norbert-walter/Windsensor_Yachta/project/cad/Gerber/Bottom_3D_Yachta.png

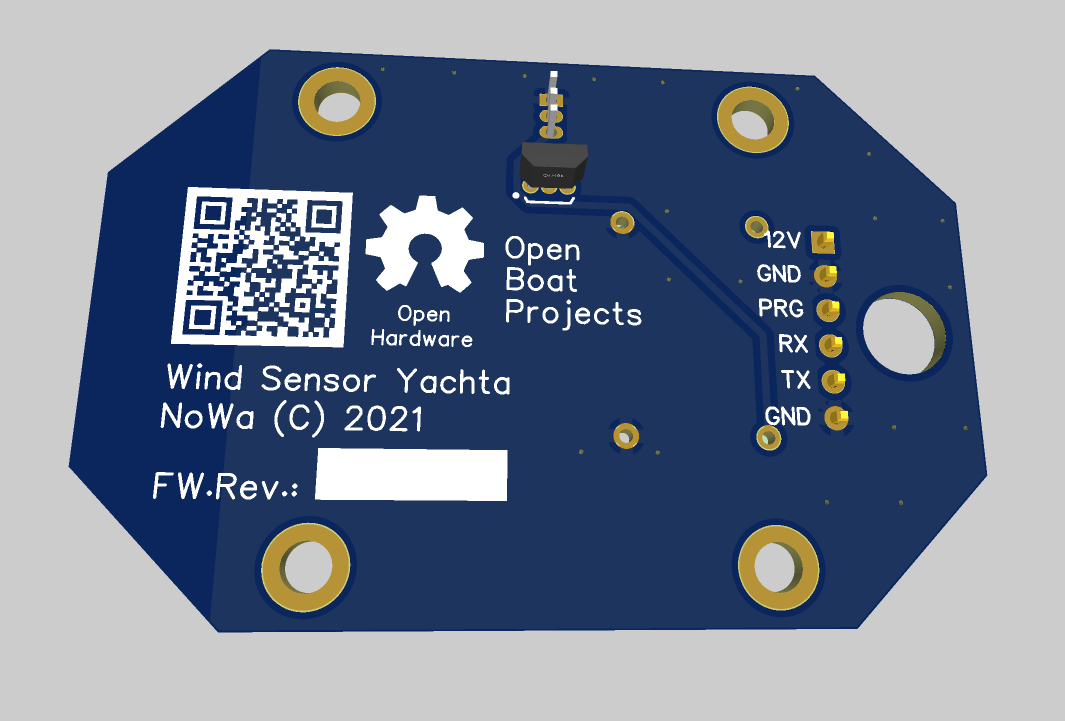
project/cad/Gerber/Bottom_3D_Yachta.png
