norbert-walter/Windsensor_Yachta/project/cad/Gerber/Top_Yachta.png

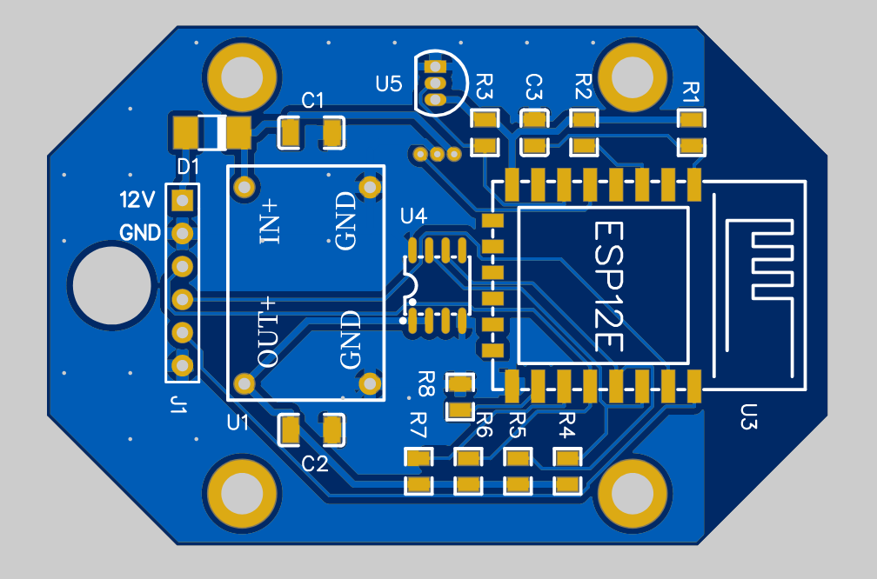
project/cad/Gerber/Top_Yachta.png
