norbert-walter/Windsensor_Yachta/project/pictures/Yachta_Thingiverse/Yachta1.png

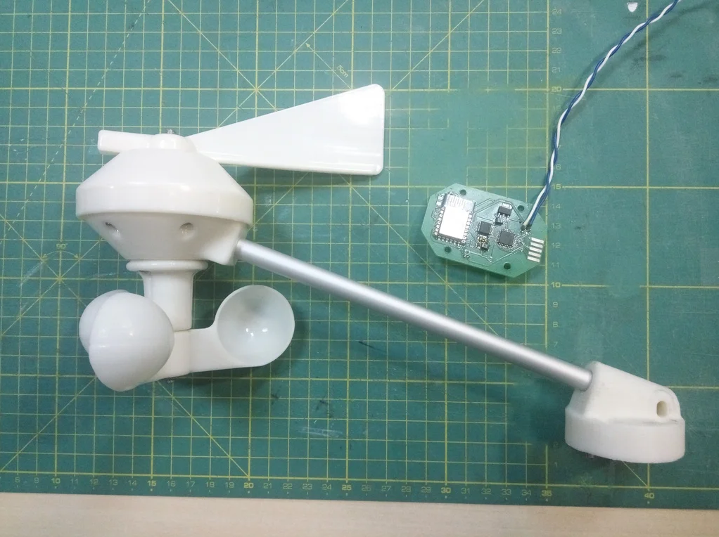
project/pictures/Yachta_Thingiverse/Yachta1.png
