norbert-walter/Windsensor_Yachta/project/pictures/Yachta_Thingiverse/Yachta2.png

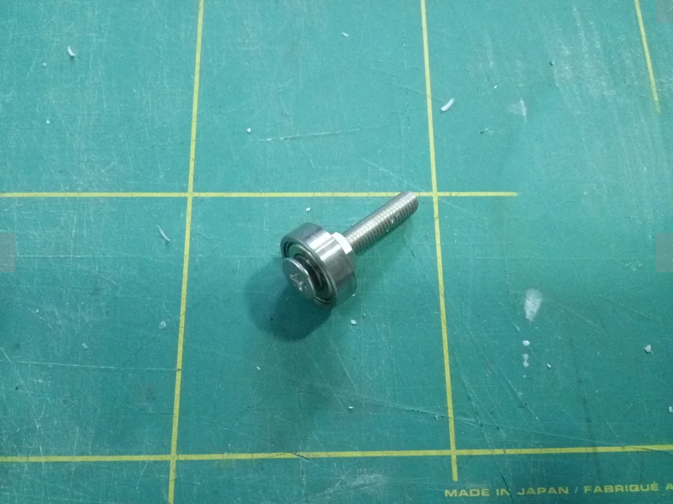
project/pictures/Yachta_Thingiverse/Yachta2.png
