norbert-walter/Windsensor_Yachta/project/pictures/Yachta_Thingiverse/Yachta3.png

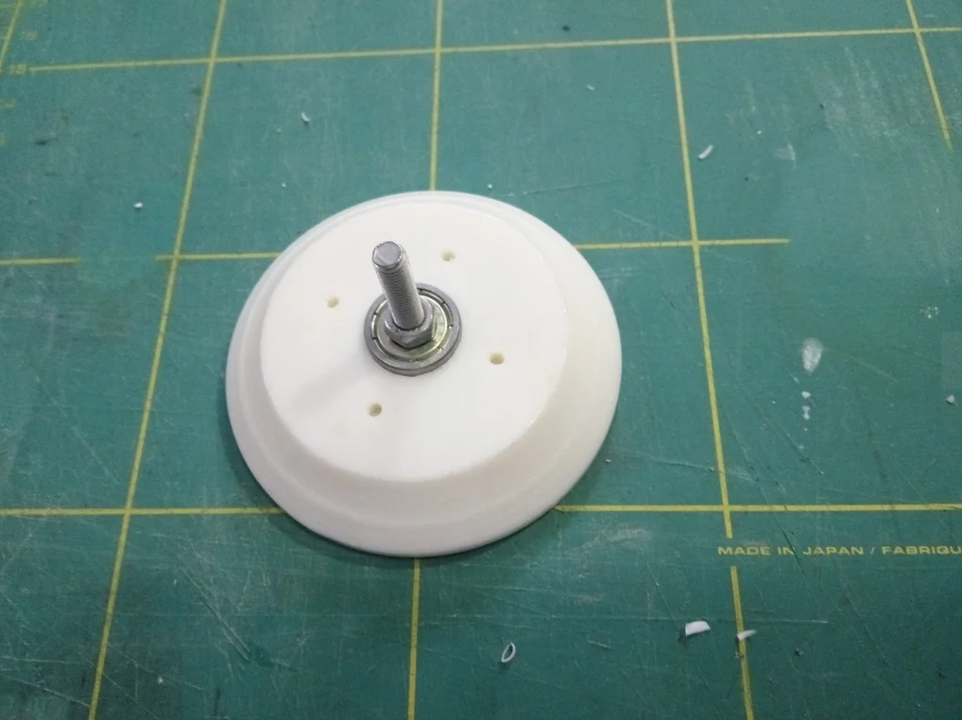
project/pictures/Yachta_Thingiverse/Yachta3.png
