norbert-walter/Windsensor_Yachta/project/pictures/Yachta_Thingiverse/Yachta5.png

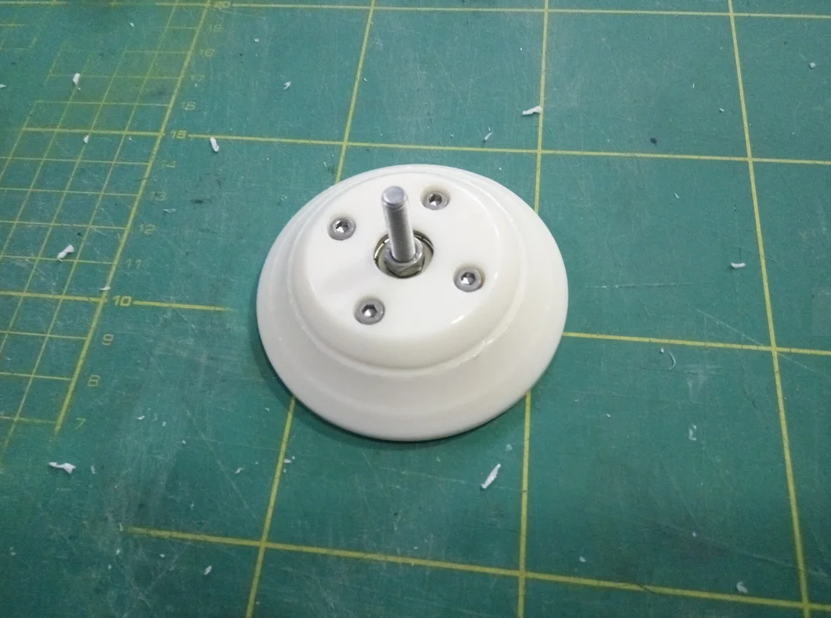
project/pictures/Yachta_Thingiverse/Yachta5.png
