norbert-walter/Windsensor_Yachta/project/pictures/Yachta_Thingiverse/Yachta7.png

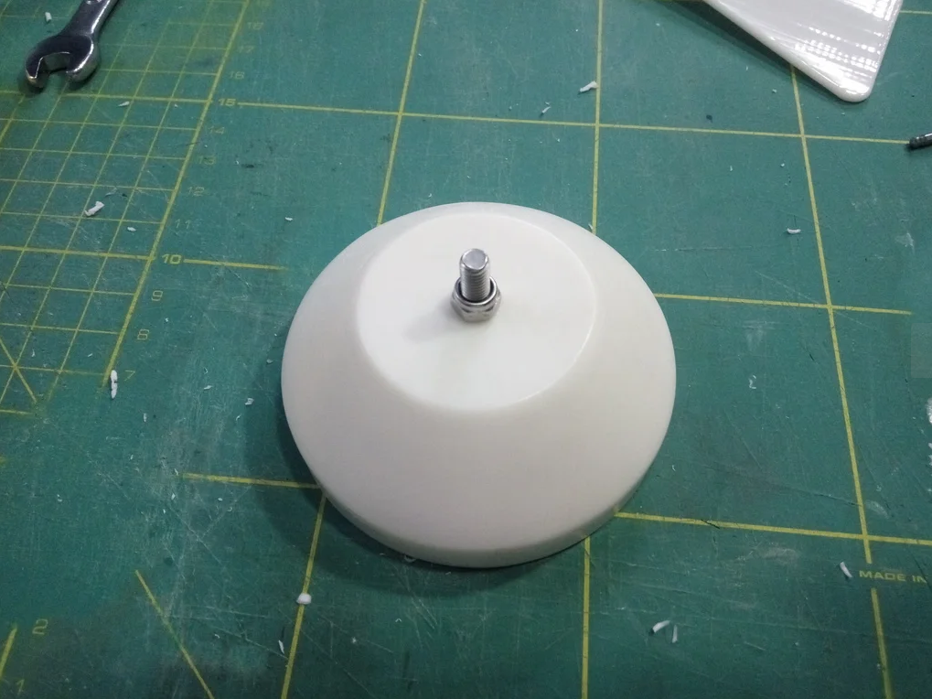
project/pictures/Yachta_Thingiverse/Yachta7.png
