norbert-walter/Windsensor_Yachta/project/pictures/Yachta_Thingiverse/Yachta8.png

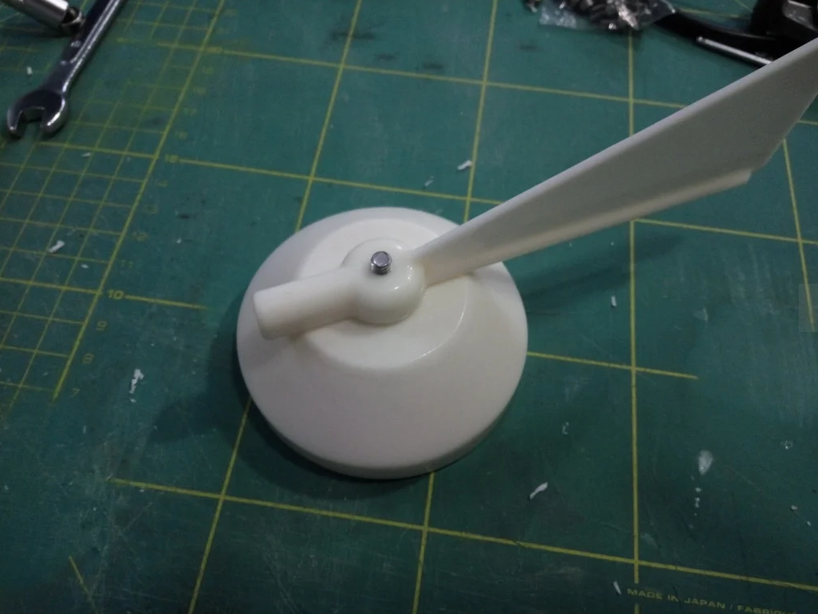
project/pictures/Yachta_Thingiverse/Yachta8.png
