norbert-walter/Windsensor_Yachta/project/pictures/Yachta_Thingiverse/Yachta10.png

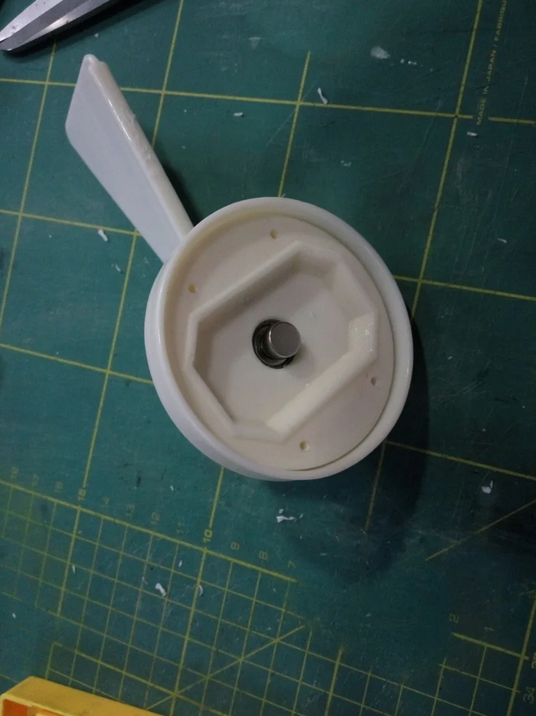
project/pictures/Yachta_Thingiverse/Yachta10.png
