norbert-walter/Windsensor_Yachta/project/pictures/Yachta_Thingiverse/Yachta11.png

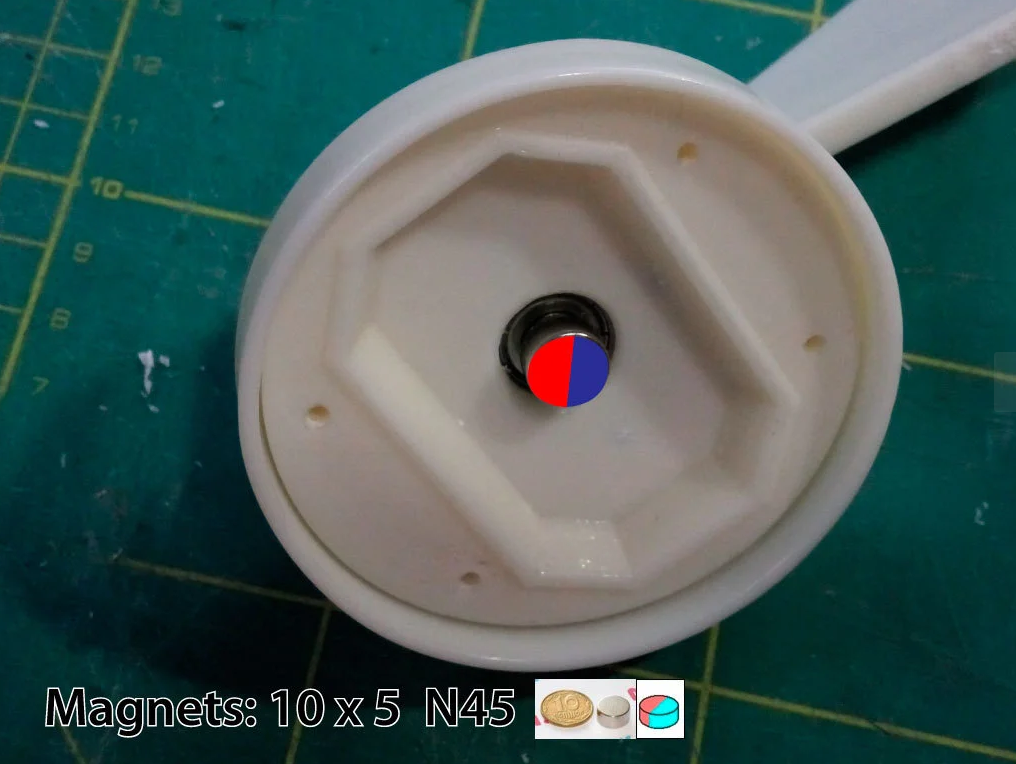
project/pictures/Yachta_Thingiverse/Yachta11.png
