norbert-walter/Windsensor_Yachta/project/pictures/Yachta_Thingiverse/Yachta13.png

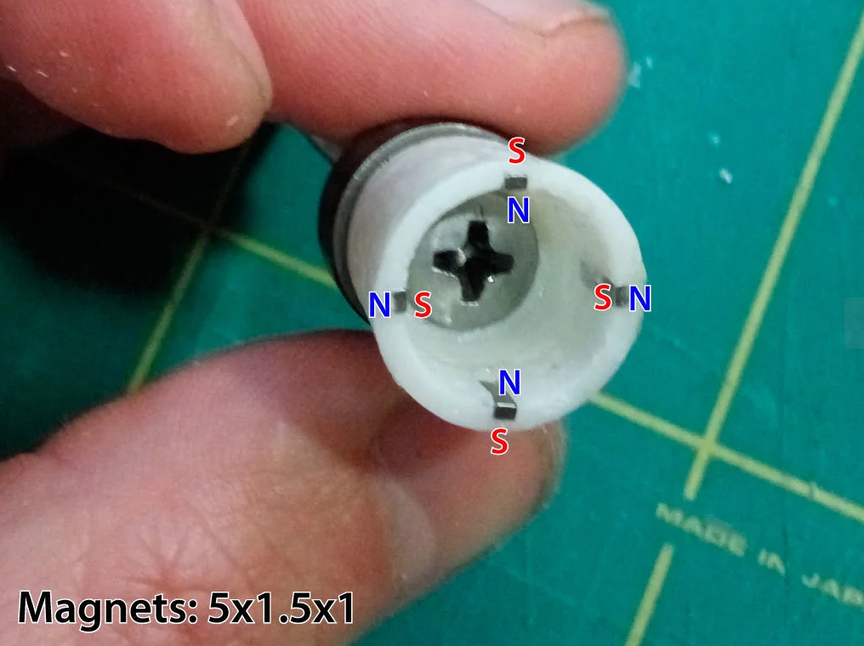
project/pictures/Yachta_Thingiverse/Yachta13.png
