norbert-walter/Windsensor_Yachta/project/pictures/Yachta_Thingiverse/Yachta14.png

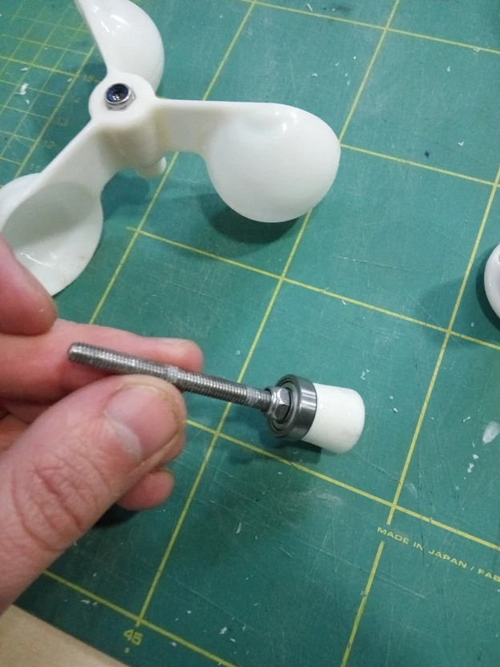
project/pictures/Yachta_Thingiverse/Yachta14.png
