norbert-walter/Windsensor_Yachta/project/pictures/Yachta_Thingiverse/Yachta15.png

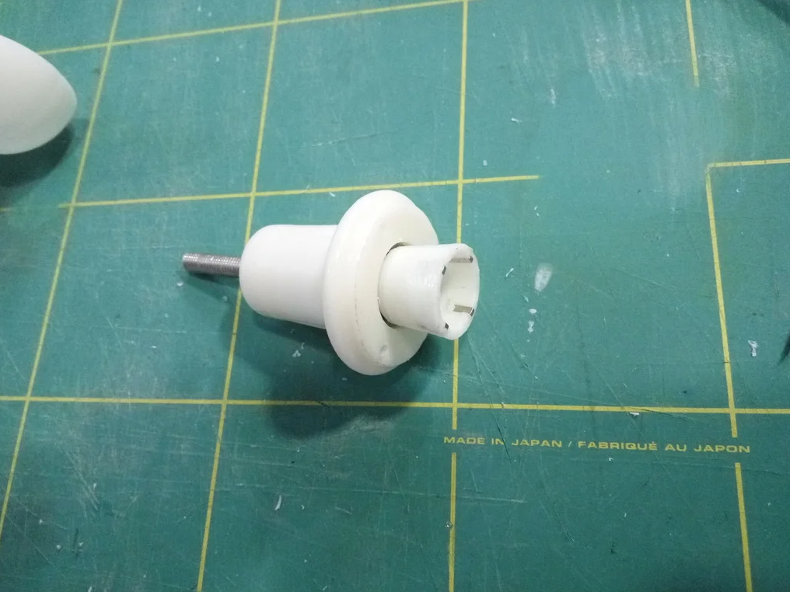
project/pictures/Yachta_Thingiverse/Yachta15.png
