norbert-walter/Windsensor_Yachta/project/pictures/Yachta_Thingiverse/Yachta16.png

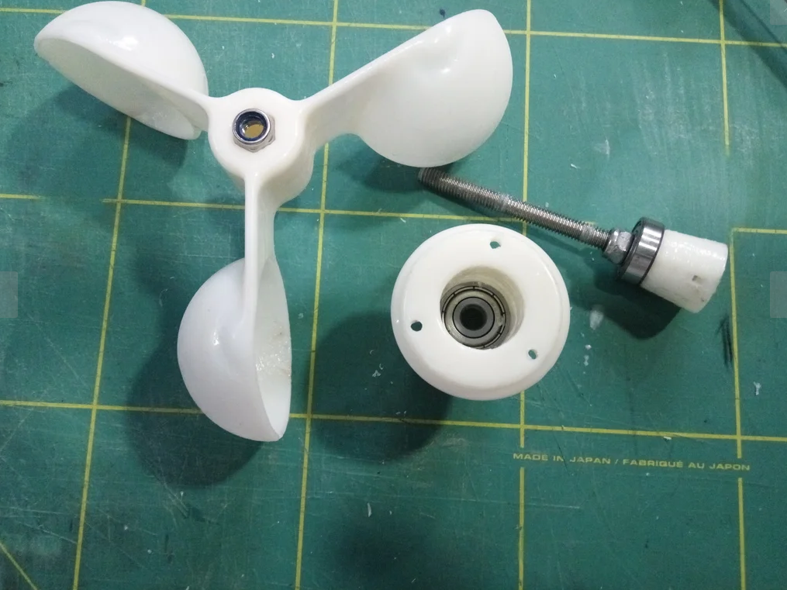
project/pictures/Yachta_Thingiverse/Yachta16.png
