norbert-walter/Windsensor_Yachta/project/pictures/Yachta_Thingiverse/Yachta17.png

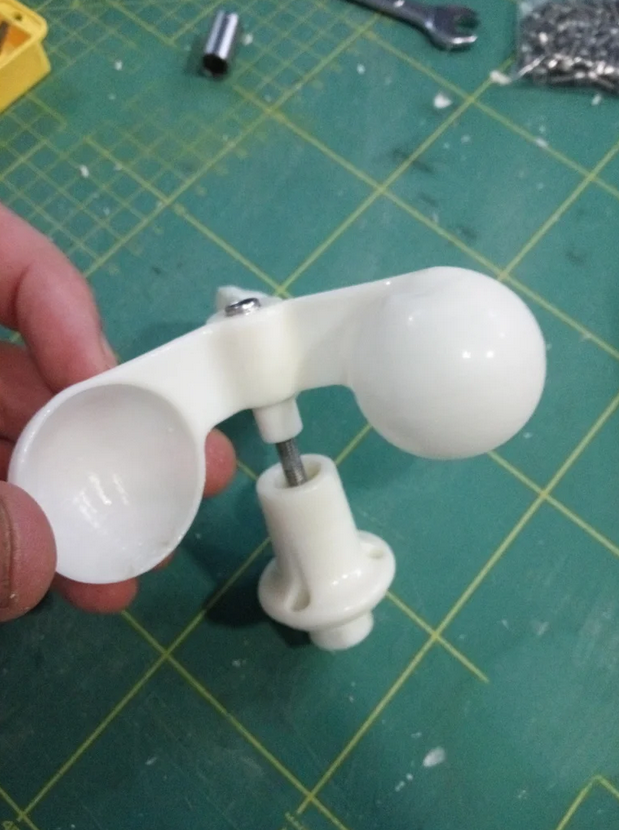
project/pictures/Yachta_Thingiverse/Yachta17.png
