norbert-walter/Windsensor_Yachta/project/pictures/Yachta_Thingiverse/Yachta18.png

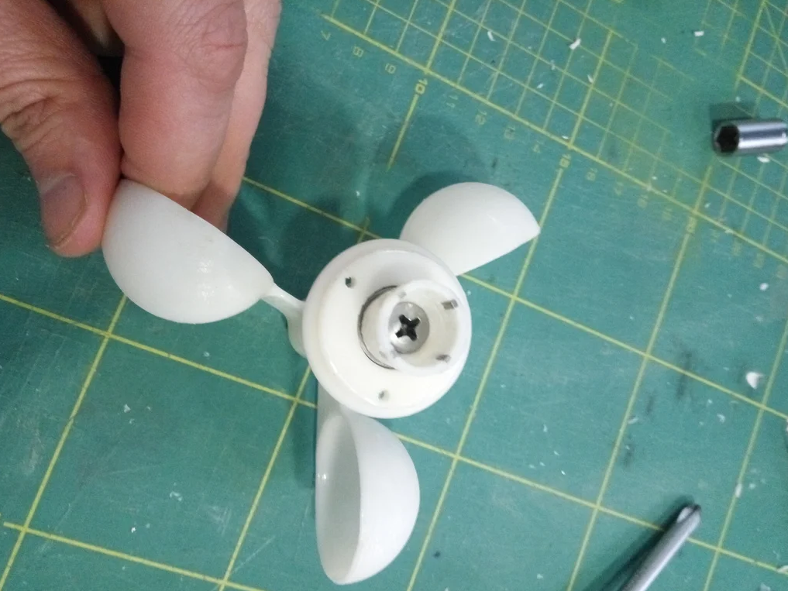
project/pictures/Yachta_Thingiverse/Yachta18.png
