norbert-walter/Windsensor_Yachta/project/pictures/Yachta_Thingiverse/Yachta19.png

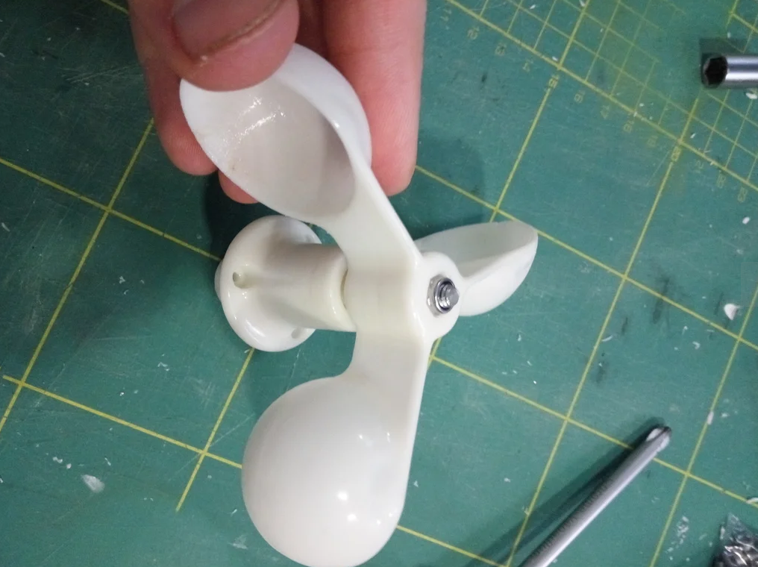
project/pictures/Yachta_Thingiverse/Yachta19.png
