norbert-walter/Windsensor_Yachta/project/pictures/Yachta_Thingiverse/Yachta20.png

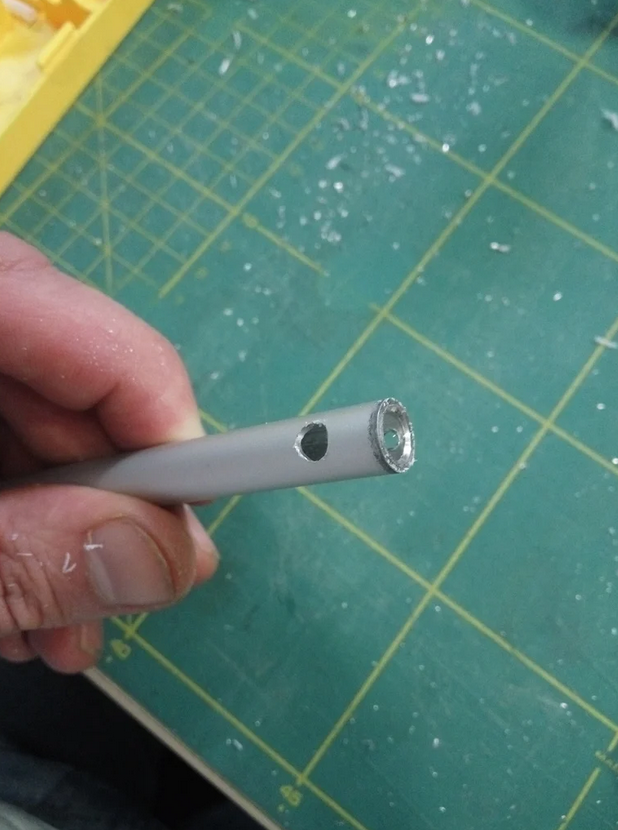
project/pictures/Yachta_Thingiverse/Yachta20.png
