norbert-walter/Windsensor_Yachta/project/pictures/Yachta_Thingiverse/Yachta21.png

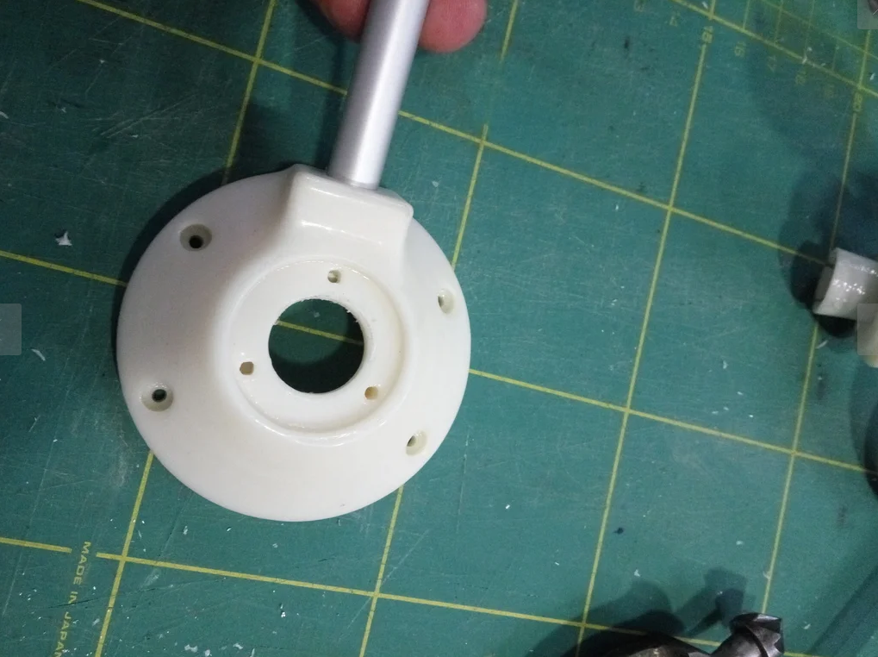
project/pictures/Yachta_Thingiverse/Yachta21.png
