norbert-walter/Windsensor_Yachta/project/pictures/Yachta_Thingiverse/Yachta22.png

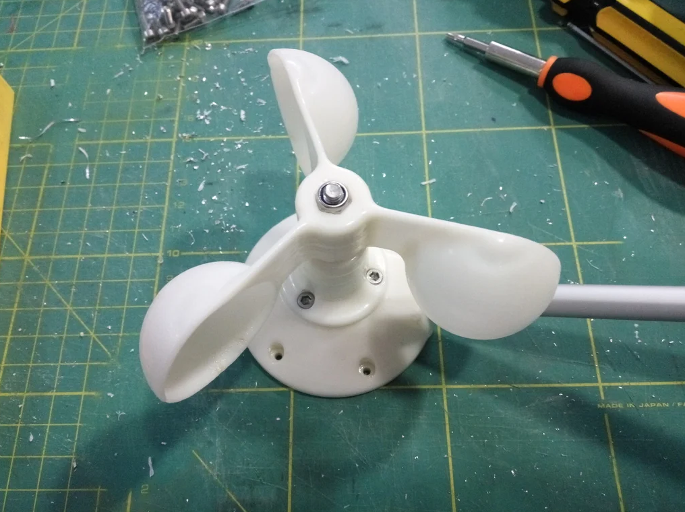
project/pictures/Yachta_Thingiverse/Yachta22.png
