norbert-walter/Windsensor_Yachta/project/pictures/Yachta_Thingiverse/Yachta23.png

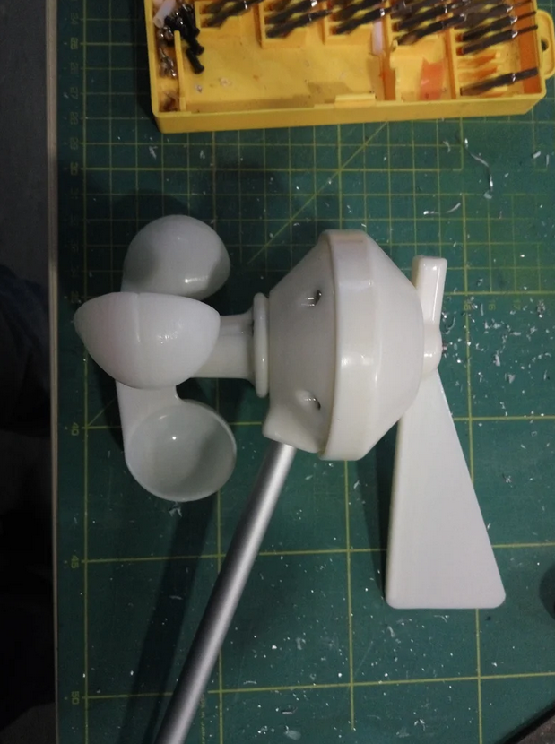
project/pictures/Yachta_Thingiverse/Yachta23.png
