norbert-walter/Windsensor_Yachta/project/cad/3D-Parts/base_power.stl

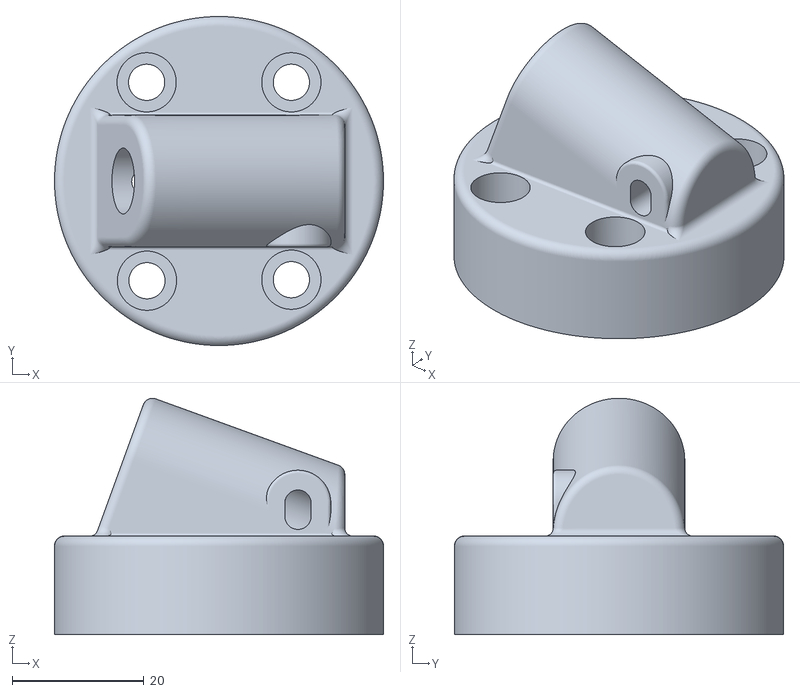
[picture p48: CAD file, 2023-07-21]
project/cad/3D-Parts/base_power.stl
50.0 x 50.0 x 35.9
