norbert-walter/Windsensor_Yachta/project/cad/Mechanics/IGES/Loeffel_spitz v1.iges

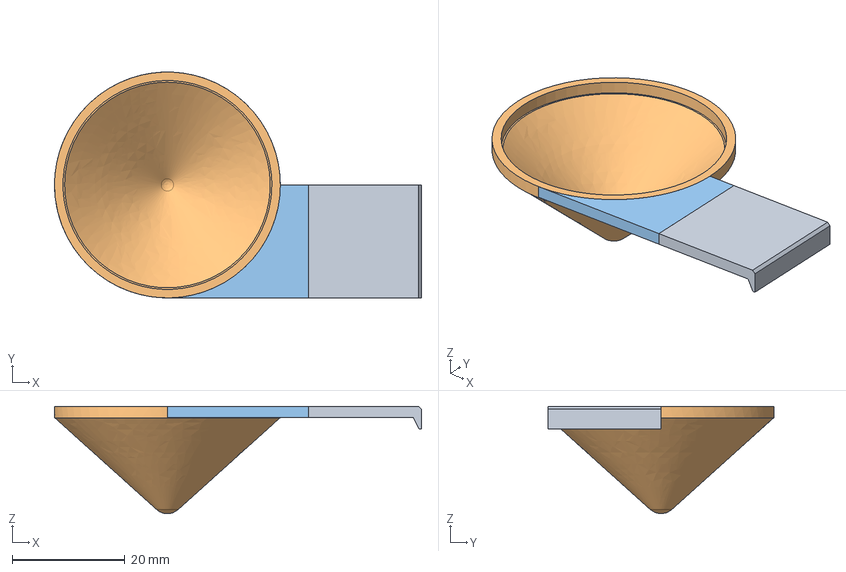
[picture p49: CAD file, 2023-07-21]
project/cad/Mechanics/IGES/Loeffel_spitz v1.iges
65.0 x 40.0 x 19.0 mm
