norbert-walter/Windsensor_Yachta/project/cad/Mechanics/IGES/Magnethalter.iges

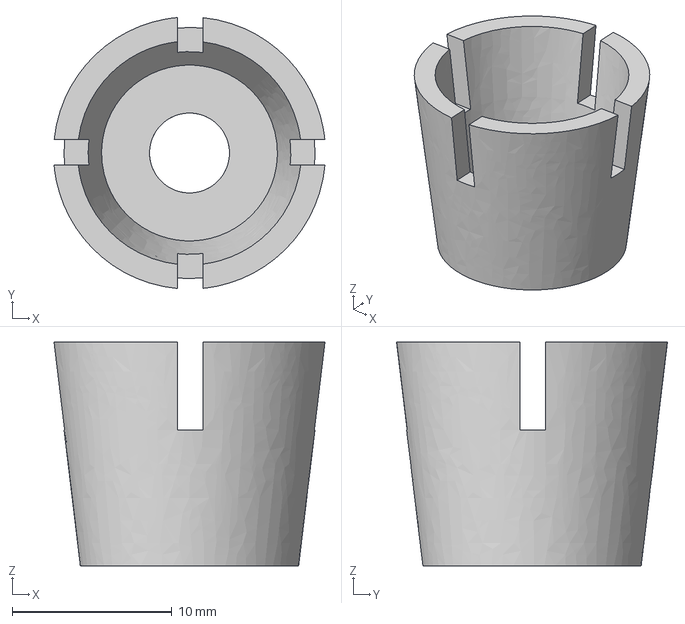
[picture p50: CAD file, 2023-07-21]
project/cad/Mechanics/IGES/Magnethalter.iges
17.0 x 17.0 x 14.0 mm
