norbert-walter/Windsensor_Yachta/project/cad/3D-Parts/top_1.stl

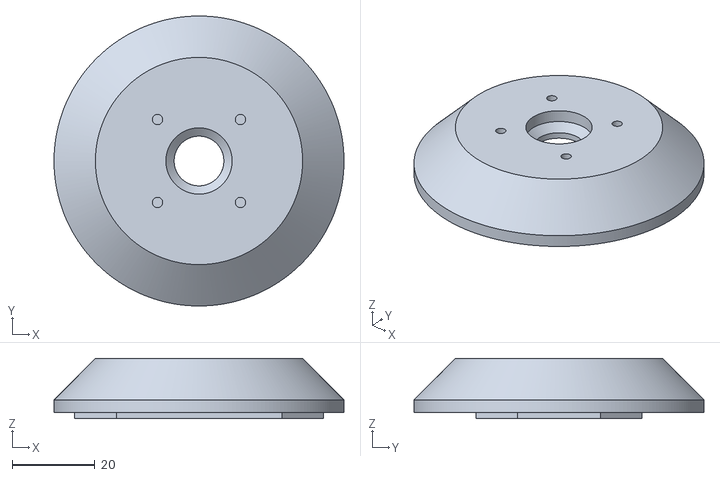
[picture p51: CAD file, 2023-07-21]
project/cad/3D-Parts/top_1.stl
70.0 x 70.0 x 14.5
