norbert-walter/Windsensor_Yachta/project/cad/3D-Parts/top_2.stl

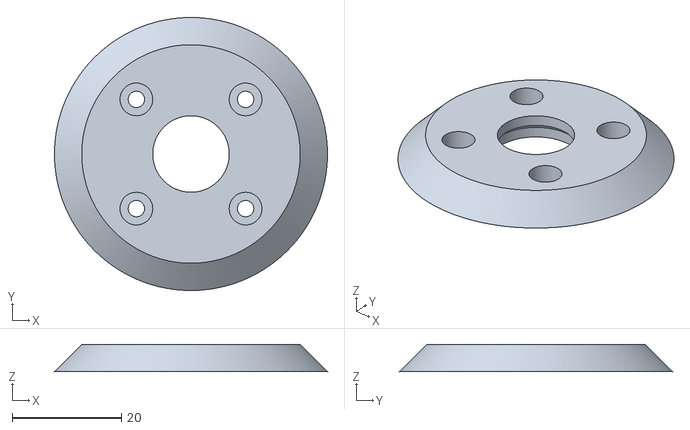
[picture p52: CAD file, 2023-07-21]
project/cad/3D-Parts/top_2.stl
50.0 x 50.0 x 5.00
