norbert-walter/Windsensor_Yachta/project/cad/3D-Parts/Print_Position.jpg

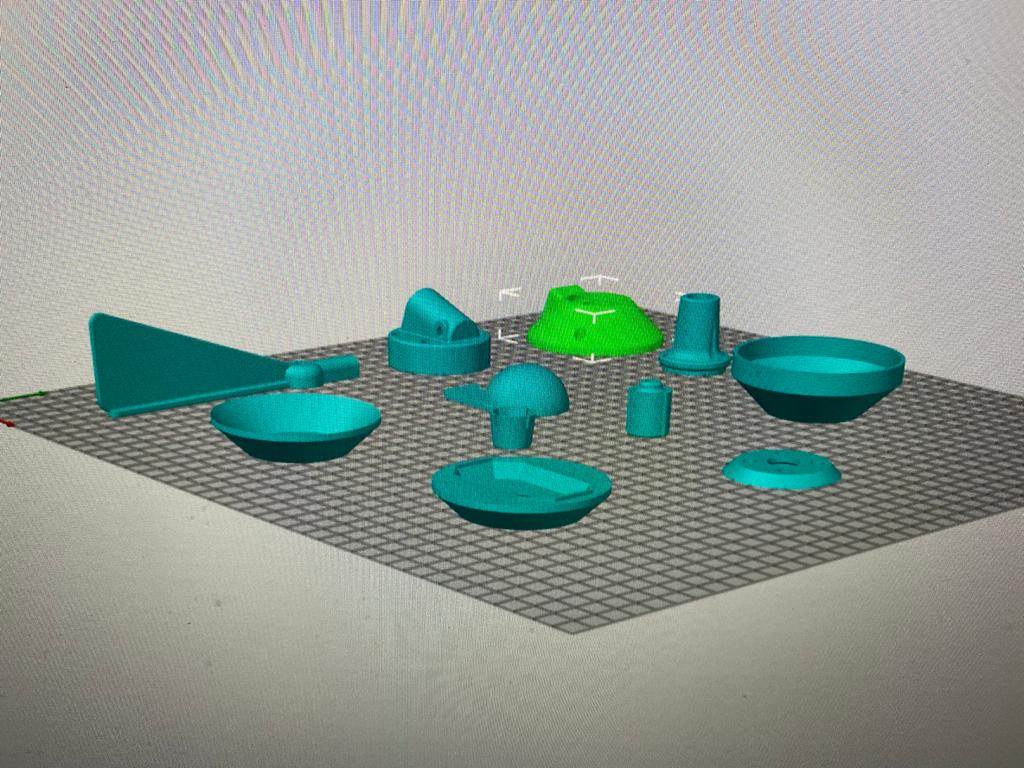
project/cad/3D-Parts/Print_Position.jpg
