norbert-walter/Windsensor_Yachta/project/pictures/Yachta_Thingiverse/Assembly2.png

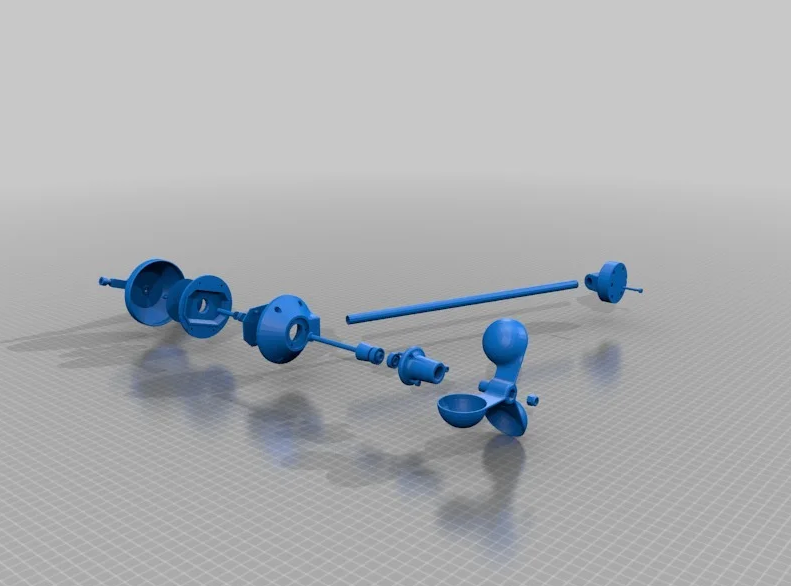
project/pictures/Yachta_Thingiverse/Assembly2.png
