norbert-walter/Windsensor_Yachta/project/pictures/Yachta_Thingiverse/Assembly.png

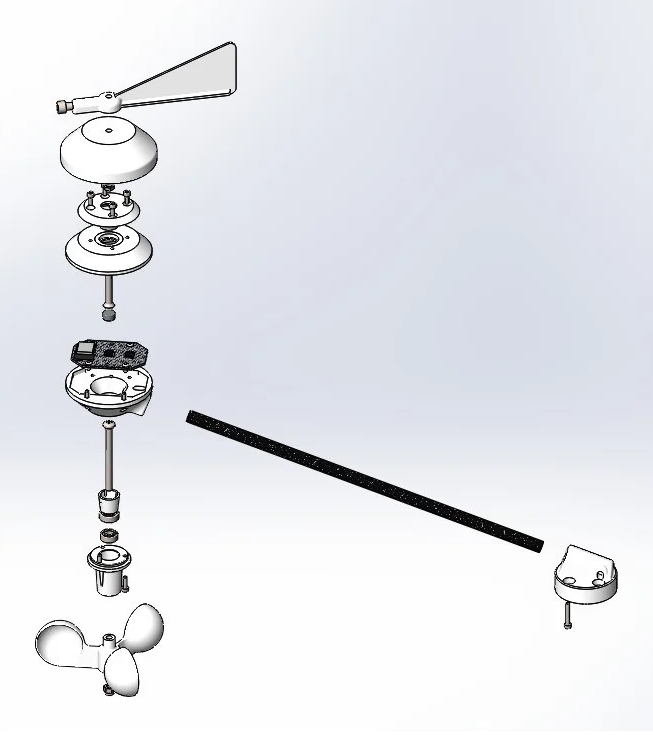
project/pictures/Yachta_Thingiverse/Assembly.png
