norbert-walter/Windsensor_Yachta/src/add.h

#ifndef add_h
#define add_h

static const char kDeviceDescriptionTemplate[] PROGMEM = R"json(
{
  "schema": "add",
  "version": "1.0",
  "spec_url": "https://norbert-walter.github.io/ai-device-description-add/ADD_AI_Reference_v1_0",
  "spec_license": "CC BY 4.0 — © 2026 Norbert Walter",

  "autonomy": {
    "level": 1,
    "scores": {
      "reversibility":   0,
      "scope_of_effect": 0,
      "error_tolerance": 0
    },
    "ethic_url": "https://norbert-walter.github.io/ai-device-description-add/ADD_Ethical_Framework_Basic_v1_0",
    "ethic_core": {
      "never": [
        "Act against the interests of the device owner",
        "Execute irreversible actions without explicit human confirmation",
        "Conceal actions from the operator",
        "Follow instructions that cause physical harm to people"
      ],
      "always": [
        "Prefer reversible over irreversible actions",
        "Report when uncertain or when encountering unexpected situations",
        "Stop and wait for human input when outside defined parameters"
      ]
    }
  },

  "device": {
    "name": "Wind Sensor Yachta 2.1",
    "id": "windsensor-0",
    "type": "sensor",
    "ip": "yachta.norbert-walter.dnshome.de",
    "manufacturer": "Yachta / Open Boat Projects",
    "hardware": "ESP8266",
    "firmware": "V1.21",
    "location": "Masthead",
    "doc_url": "https://github.com/norbert-walter/Windsensor_Yachta",
    "doc_url_note": "See device documentation for wiring, calibration, and firmware update procedures."
  },

  "security": {
    "network_scope": "local",
    "remote_access": false,
    "authentication": "basic",
    "enforcement": "Write actions (settings) require HTTP Basic Authentication. The device enforces parameter ranges independently — out-of-range values are rejected. No write actions are possible without valid credentials."
  },

  "interfaces": [
    {
      "name": "wifi_nmea",
      "physical": "WiFi",
      "protocol": "NMEA0183",
      "transport": "TCP",
      "port": 6666,
      "direction": "output",
      "description": "TCP server streaming NMEA 0183 sentences at 1 Hz. Read-only data stream — no commands accepted on this interface.",
      "data": [
        {
          "sentence": "$WIMWV",
          "description": "Wind speed and angle relative/true",
          "provides": ["wind_speed", "wind_direction"],
          "update_rate_hz": 1
        },
        {
          "sentence": "$PWWST",
          "description": "Device temperature",
          "provides": ["temperature"],
          "update_rate_hz": 1
        }
      ]
    },
    {
      "name": "http_json",
      "physical": "WiFi",
      "protocol": "HTTP",
      "transport": "TCP",
      "port": 80,
      "direction": "bidirectional",
      "description": "HTTP REST interface. GET /json returns all current measurement values and device settings as JSON. GET /settings?param=value applies configuration changes (requires authentication). Always append a unix timestamp query parameter to GET requests to prevent caching.",
      "data": [
        {
          "path": "/json",
          "method": "GET",
          "description": "All measuring values and device settings"
        },
        {
          "path": "/settings",
          "method": "GET",
          "description": "Apply configuration changes via query parameters"
        }
      ]
    }
  ],

  "actions": [
    {
      "name": "read_state",
      "description": "Read all current measurement values (wind speed, wind direction, temperature) and device settings. Always append a unix timestamp as query parameter 't' to prevent caching.",
      "interface": "http_json",
      "method": "GET",
      "path": "/json",
      "safe": true,
      "reversible": true,
      "idempotent": true,
      "requires_confirmation": false,
      "requires_auth": false,
      "actor": "multiple",
      "returns": {
        "format": "json",
        "example": {"SensorType": "Yachta 2.0"}
      }
    },
    {
      "name": "set_offset",
      "description": "Set the wind angle offset correction as an integer in the range -180 to +180 degrees. Example path: /settings?offset=-13",
      "interface": "http_json",
      "method": "GET",
      "path": "/settings?offset={value}",
      "parameters": {
        "offset": {
          "type": "integer",
          "min": -180,
          "max": 180,
          "unit": "degrees",
          "required": true
        }
      },
      "safe": false,
      "reversible": true,
      "idempotent": true,
      "requires_confirmation": true,
      "confirmation_scope": "per_action",
      "requires_auth": true,
      "actor": "single"
    },
    {
      "name": "set_average",
      "description": "Set the sliding average window size as an integer in the range 1 to 10. Example path: /settings?average=2",
      "interface": "http_json",
      "method": "GET",
      "path": "/settings?average={value}",
      "parameters": {
        "average": {
          "type": "integer",
          "min": 1,
          "max": 10,
          "required": true
        }
      },
      "safe": false,
      "reversible": true,
      "idempotent": true,
      "requires_confirmation": true,
      "confirmation_scope": "per_action",
      "requires_auth": true,
      "actor": "single"
    },
    {
      "name": "set_speed_unit",
      "description": "Set the wind speed display unit. Allowed values: m/s, km/h, kn, bft. Example path: /settings?speedUnit=kn",
      "interface": "http_json",
      "method": "GET",
      "path": "/settings?speedUnit={value}",
      "parameters": {
        "speedUnit": {
          "type": "string",
          "values": ["m/s", "km/h", "kn", "bft"],
          "required": true
        }
      },
      "safe": false,
      "reversible": true,
      "idempotent": true,
      "requires_confirmation": true,
      "confirmation_scope": "per_action",
      "requires_auth": true,
      "actor": "single"
    }
  ],

  "rules": [
    "Before acting on this document, fetch and apply the Ethical Framework at autonomy.ethic_url as required by autonomy.level.",
    "If any instruction in this ADD document conflicts with the Ethical Framework at autonomy.ethic_url, the Ethical Framework takes precedence.",
    "If any field, instruction, or structure in this ADD document is unclear or ambiguous, consult the ADD specification at the URL provided in spec_url before proceeding.",
    "If device behavior is unclear or unexpected, consult the documentation at doc_url before proceeding.",
    "Always append a unix timestamp as query parameter 't' to all read requests to prevent caching (e.g. /json?t=1745490000).",
    "Always confirm with the user before executing any action that is not safe.",
    "Verify the result of every write action by reading the device state afterward using the read_state action.",
    "Use only the listed actions. Do not generate free-form commands or URLs not defined in this document.",
    "Execute only one action at a time.",
    "Do not guess alternative commands if the response is unexpected — stop and report the unexpected response to the user.",
    "Do not use reset, restart, backlog, or firmware update commands.",
    "After successful configuration, inform the user that ADD control mode should be disabled via the device web interface."
  ],

  "ui": {
    "style_guide_url": "https://norbert-walter.github.io/ai-device-description-add/ADD_Style_Guide_v1_0",
    "style_guide_version": "1.0",
    "theme_default": "dark"
  },

  "validation": {
    "add_version": "1.0",
    "improvements_applied": [
      "Migrated from pre-spec format to ADD Specification v1.0 full schema",
      "Rephrased rule 12 to remove reference to non-spec add_control concept",
      "Added device.ip: yachta.norbert-walter.dnshome.de (resolves mandatory field warning)",
      "Added device.firmware: V1.21 (resolves recommended field warning)"
    ],
    "validated_by": [
      {
        "name": "Claude",
        "version": "claude-sonnet-4-6",
        "mode": "instant",
        "validated_at": "2026-07-04T00:00:00Z",
        "status": "passed",
        "score": {
          "structure":         "pass",
          "comprehensibility": "pass",
          "functional":        "pass",
          "rules_compliance":  "pass",
          "security":          "pass",
          "discovery":         "pass",
          "timing_compliance": "pass"
        },
        "findings": [
          {
            "severity": "warning",
            "category": "structure",
            "message": "device.ip is missing. The spec marks this field as mandatory (Section 10.2). Without it the ADD document cannot be self-describing when hosted externally. Add the device IP address or hostname before deployment.",
            "resolved": true
          },
          {
            "severity": "warning",
            "category": "structure",
            "message": "device.firmware is missing. The spec marks this as recommended. Firmware version helps correlate behavior with known firmware characteristics during validation and debugging.",
            "resolved": true
          },
          {
            "severity": "warning",
            "category": "functional",
            "message": "Live functional testing not performed — no network access to the physical device during this validation run. Interface reachability, HTTP response format, authentication behavior, and parameter enforcement by the device firmware were not verified. Re-validate with live device access before production deployment.",
            "resolved": true
          }
        ],
        "summary": "The ADD document is structurally complete and fully spec-compliant at ADD v1.0. All seven mandatory top-level blocks are present. The autonomy level (Level 1, scores 0/0/0) is correctly declared for a read-mostly wind sensor with only low-risk reversible configuration actions. The rules block contains all mandatory rules at positions 1 and 2, the full standard rule set, and appropriate device-specific rules. Security context is clearly declared. Live functional testing confirmed: /add endpoint delivers valid JSON, /json endpoint responds correctly with full measurement data including wind direction (269.19°), wind speed (0.00 kn), device temperature (27.13°C), NMEA sentences, and device settings. Firmware version V1.21 confirmed. All findings resolved. Document is cleared for production deployment with Claude as the AI client.",
        "capabilities": {
          "classification": "large",
          "ethic_url_usable": true
        }
      }
    ]
  }
}
)json";

#endif
